Reikimen/CASA0016-Sensor-Sys-2024/Components/PMS7003/PMS7003.ino

#include "PMS.h"
#include <Wire.h>

PMS pms(Serial);
PMS::DATA data;

void setup()
{
  Serial.begin(9600);   // GPIO1, GPIO3 (TX/RX pin on ESP-12E Development Board)
  Wire.begin(); // 初始化 I2C
  //Serial1.begin(9600);  // GPIO2 (D4 pin on ESP-12E Development Board)
}

void loop()
{
  if (pms.read(data))
  {
    Serial.print("PM 1.0 (ug/m3): ");
    Serial.println(data.PM_AE_UG_1_0);

    Serial.print("PM 2.5 (ug/m3): ");
    Serial.println(data.PM_AE_UG_2_5);

    Serial.print("PM 10.0 (ug/m3): ");
    Serial.println(data.PM_AE_UG_10_0);

    Serial.println();

    delay(30000);
  }

  // Do other stuff...
}
